JorgeMarin5692/Robotica_Industrial/Disenio 3D/servoMG996R/MG996R Servo Motor/Servo Horns.SLDPRT

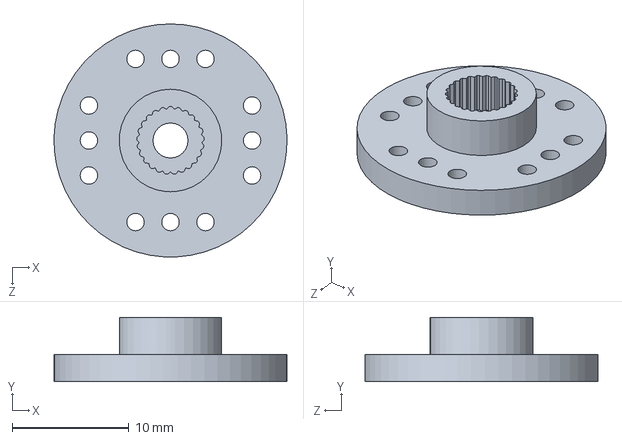
[picture p25: CAD file, 2024-06-09]
Disenio 3D/servoMG996R/MG996R Servo Motor/Servo Horns.SLDPRT
20.0 x 5.50 x 20.0 mm
