JorgeMarin5692/Robotica_Industrial/Disenio 3D/Base2.SLDPRT

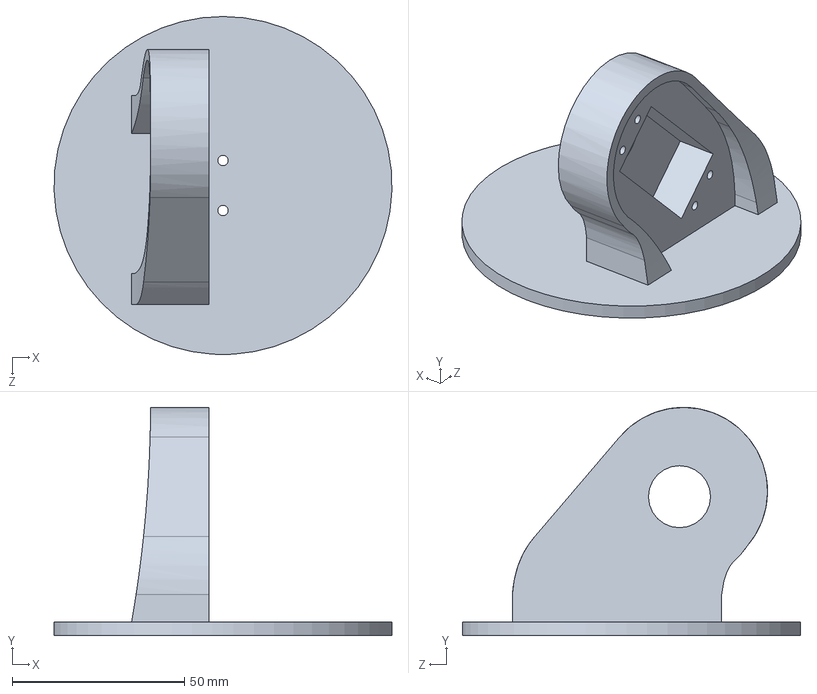
[picture p26: CAD file, 2024-06-09]
Disenio 3D/Base2.SLDPRT
98.0 x 66.2 x 98.0 mm
