JorgeMarin5692/Robotica_Industrial/Disenio 3D/servoMG996R/MG996R Servo Motor/Case.SLDPRT

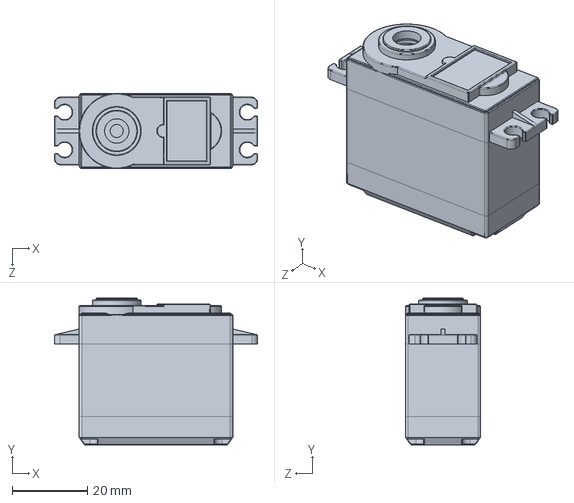
[picture p27: CAD file, 2024-06-09]
Disenio 3D/servoMG996R/MG996R Servo Motor/Case.SLDPRT
54.0 x 39.0 x 20.0 mm
