JorgeMarin5692/Robotica_Industrial/Disenio 3D/eslabon 1.SLDPRT

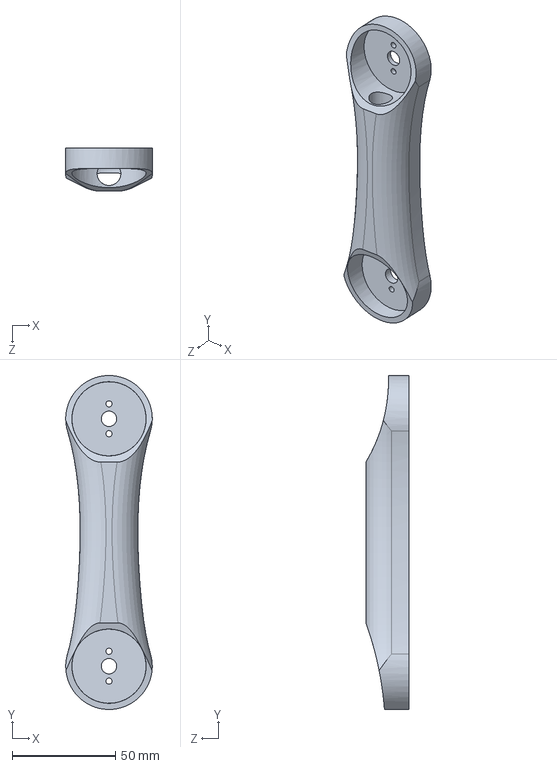
[picture p28: CAD file, 2024-06-09]
Disenio 3D/eslabon 1.SLDPRT
42.0 x 162.0 x 21.0 mm
