JorgeMarin5692/Robotica_Industrial/Disenio 3D/Gripper link.SLDPRT

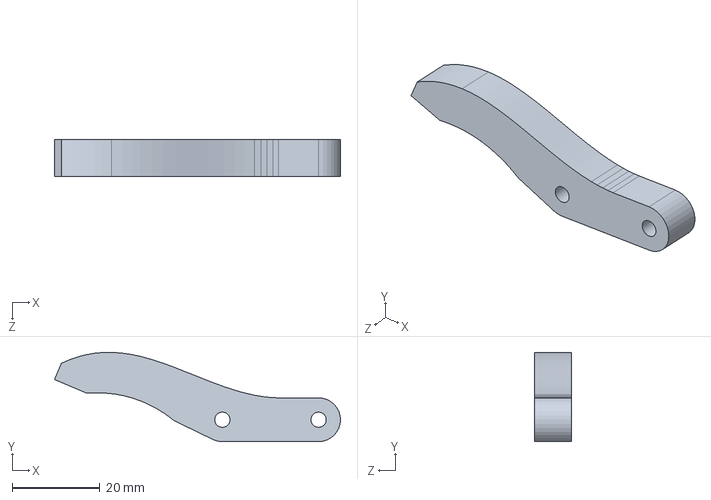
[picture p29: CAD file, 2024-06-09]
Disenio 3D/Gripper link.SLDPRT
65.3 x 20.4 x 8.50 mm
