JorgeMarin5692/Robotica_Industrial/Disenio 3D/ARM2.SLDPRT

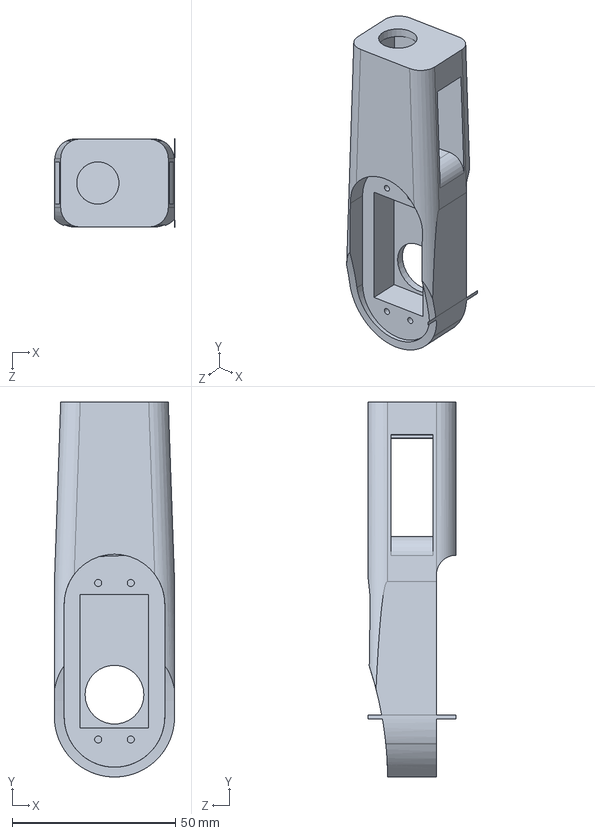
[picture p30: CAD file, 2024-06-09]
Disenio 3D/ARM2.SLDPRT
36.9 x 115.0 x 27.0 mm
